LouWii/ErgoMax/Case/Acrylic/MakersLabs/Layer 2.dxf

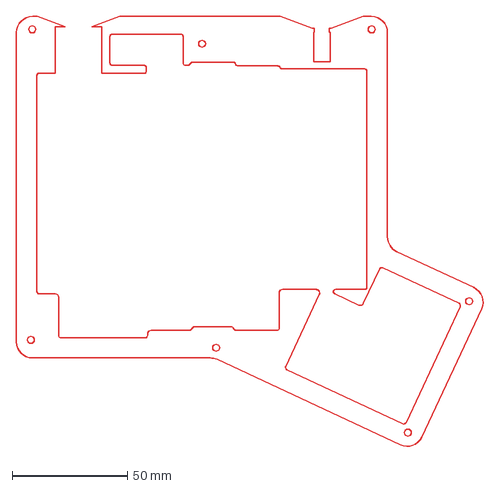
[picture p9: CAD file, 2023-05-06]
Case/Acrylic/MakersLabs/Layer 2.dxf
202.8 x 187.7 mm
